itsdmd/sofle-v1-modular-case/img/01.png

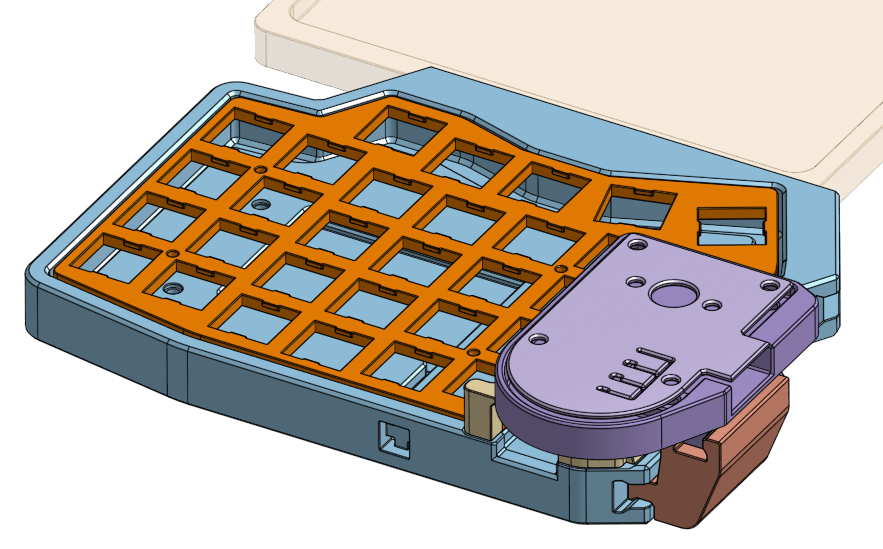
img/01.png
