itsdmd/sofle-v1-modular-case/img/02.png

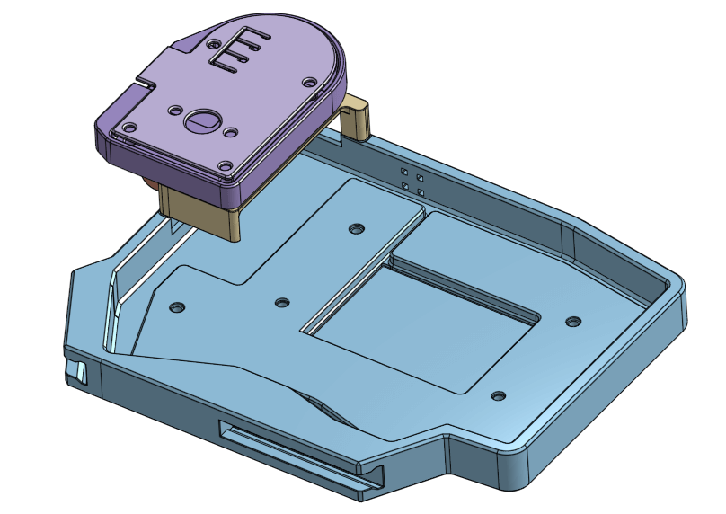
img/02.png
