itsdmd/sofle-v1-modular-case/img/06.png

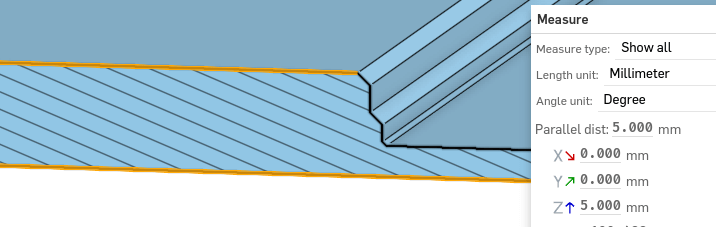
img/06.png
