itsdmd/sofle-v1-modular-case/img/6x6_button.jpeg

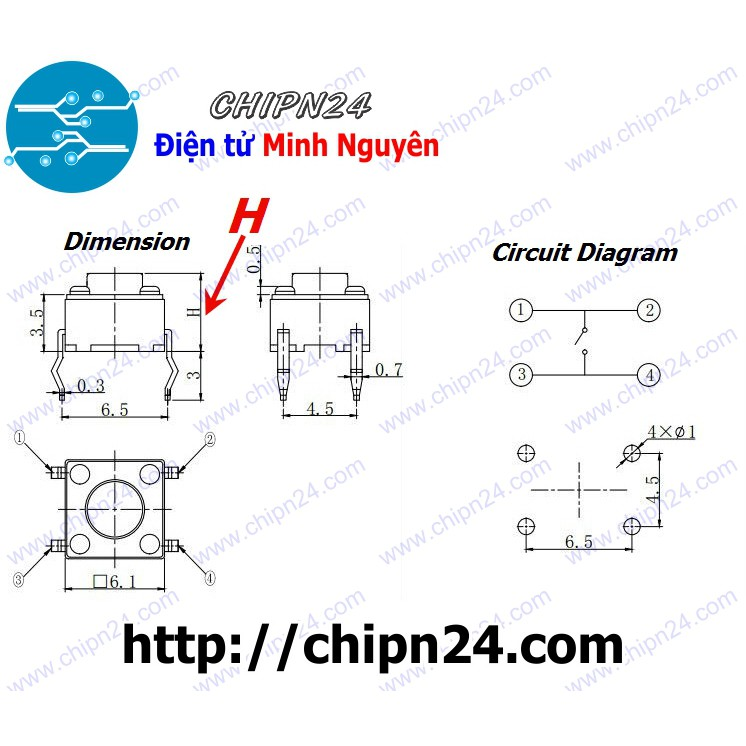
img/6x6_button.jpeg
