itsdmd/sofle-v1-modular-case/img/08.png

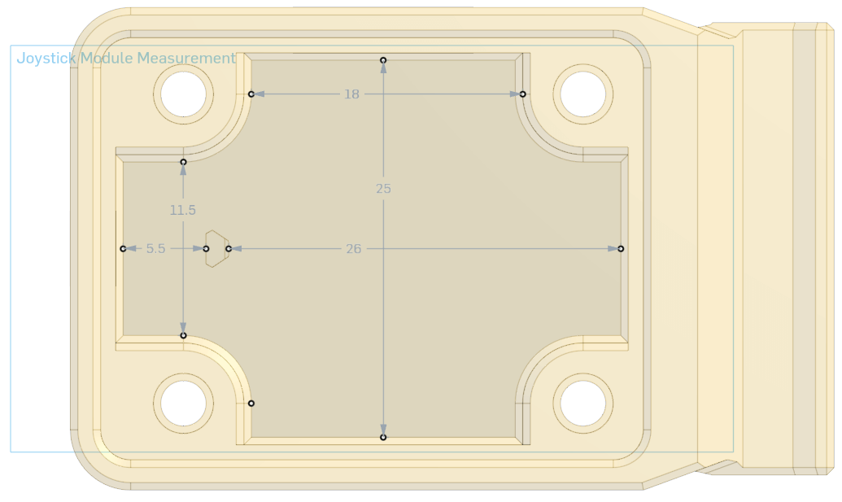
img/08.png
