itsdmd/sofle-v1-modular-case/img/09.png

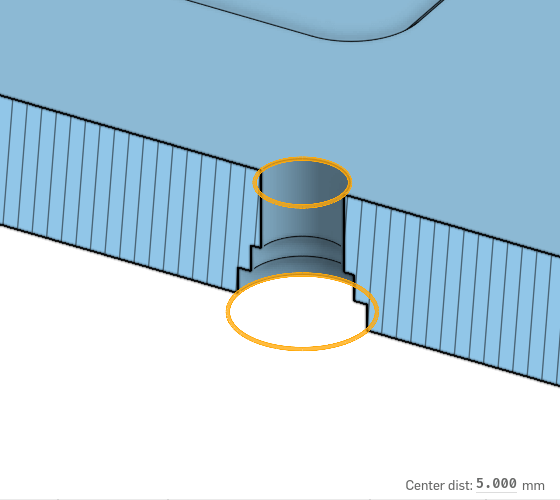
img/09.png
