itsdmd/sofle-v1-modular-case/img/rocker_trackpoint_module_modded.jpg

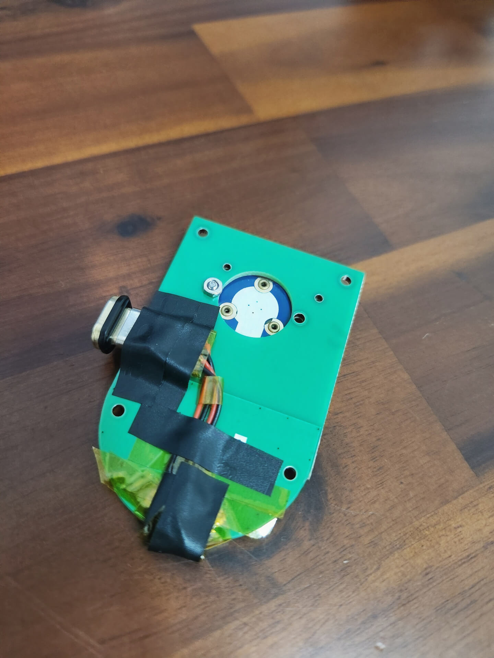
img/rocker_trackpoint_module_modded.jpg
