itsdmd/sofle-v1-modular-case/img/screw_m2.jpeg

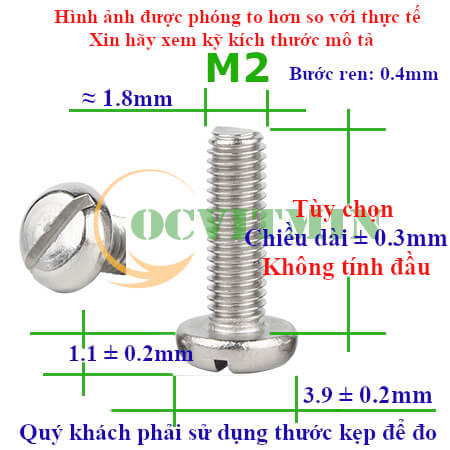
img/screw_m2.jpeg
